rtjelum/esp32-ld19-lidar/sokoban_levels.h

#pragma once

// Sokoban level data, '|'-separated, kept in flash (PROGMEM).
// Map symbols: '#' wall, ' ' floor, '.' goal, '$' box, '*' box on goal,
//              '@' player, '+' player on goal.
//
// Each level sits in its own raw-string block so the playfield reads as
// ASCII art in source — adjacent string literals concatenate, and the
// "|" between blocks is the run-time level separator.
//
// NOTE: currently unused by the firmware. The Sokoban page in sokoban_page.h
// ships its own copy of the levels in JS. Kept here for a future native
// renderer that would draw the game on the AMOLED.

#ifndef PROGMEM
#define PROGMEM
#endif

static const char ZK_LEVEL_DATA[] PROGMEM =
  // ── Level 1 ──
  R"(####
# .#
#  ###
#*@  #
#  $ #
#  ###
####)"
  "|"
  // ── Level 2 ──
  R"(######
#    #
# #@ #
# $* #
# .* #
#    #
######)"
  "|"
  // ── Level 3 ──
  R"(  ####
###  ####
#     $ #
# #  #$ #
# . .#@ #
#########)"
  "|"
  // ── Level 4 ──
  R"(########
#      #
# .**$@#
#      #
#####  #
    ####)"
  "|"
  // ── Level 5 ──
  R"( #######
 #     #
 # .$. #
## $@$ #
 #  .$. #
#      #
########)"
  "|"
  // ── Level 6 ──
  R"(###### #####
#    ###   #
# $$     #@#
# $ #...   #
#   ########
#####)"
  "|"
  // ── Level 7 ──
  R"(#######
#     #
# .$. #
# $.$ #
# .$. #
# $.$ #
#  @  #
#######)"
  "|"
  // ── Level 8 ──
  R"(  ######
  # ..@#
  # $$ #
  ## ###
   # #
   # #
#### #
#    ##
# #   #
#   # #
###   #
  #####)"
  "|"
  // ── Level 9 ──
  R"(#####
#.  ##
#@$$ #
##   #
 ##  #
  ##.#
   ###)"
  "|"
  // ── Level 10 ──
  R"(      #####
      #.  #
      #.# #
#######.# #
# @ $ $ $ #
# # # # ###
#       #
#########)"
  "|"
  // ── Level 11 ──
  R"(  ######
  #    #
  # ##@##
### # $ #
# ..# $ #
#       #
#  ######
####)"
  "|"
  // ── Level 12 ──
  R"(#####
#   ##
# $  #
## $ ####
 ###@.  #
  #  .# #
  #     #
  #######)"
  "|"
  // ── Level 13 ──
  R"(####
#. ##
#.@ #
#. $#
##$ ###
 # $  #
 #    #
 #  ###
 ####)"
  "|"
  // ── Level 14 ──
  R"(#######
#     #
# # # #
#. $*@#
#   ###
#####)"
  "|"
  // ── Level 15 ──
  R"(     ###
######@##
#    .* #
#   #   #
#####$# #
    #   #
    #####)"
  "|"
  // ── Level 16 ──
  R"( ####
 #  ####
 #     ##
## ##   #
#. .# @$##
#   # $$ #
#  .#    #
##########)"
  "|"
  // ── Level 17 ──
  R"(#####
# @ #
#...#
#$$$##
#    #
#    #
######)"
  "|"
  // ── Level 18 ──
  R"(#######
#     #
#. .  #
# ## ##
#  $ #
###$ #
  #@ #
  #  #
  ####)"
  "|"
  // ── Level 19 ──
  R"(########
#   .. #
#  @$$ #
##### ##
   #  #
   #  #
   #  #
   ####)"
  "|"
  // ── Level 20 ──
  R"(#######
#     ###
#  @$$..#
#### ## #
  #     #
  #  ####
  #  #
  ####)"
  "|"
  // ── Level 21 ──
  R"(####
#  ####
# . . #
# $$#@#
##    #
 ######)"
  "|"
  // ── Level 22 ──
  R"(#####
#   ###
#. .  #
#   # #
## #  #
 #@$$ #
 #    #
 #  ###
 ####)"
  "|"
  // ── Level 23 ──
  R"(#######
#  *  #
#     #
## # ##
 #$@.#
 #   #
 #####)"
  "|"
  // ── Level 24 ──
  R"(# #####
  #   #
###$$@#
#   ###
#     #
# . . #
#######)"
  "|"
  // ── Level 25 ──
  R"( ####
 #  ###
 # $$ #
##... #
#  @$ #
#   ###
#####)"
  "|"
  // ── Level 26 ──
  R"( #####
 # @ #
 #   #
###$ #
# ...#
# $$ #
###  #
  ####)"
  "|"
  // ── Level 27 ──
  R"(######
#   .#
# ## ##
#  $$@#
# #   #
#.  ###
#####)"
  "|"
  // ── Level 28 ──
  R"(#####
#   #
# @ #
# $$###
##. . #
 #    #
 ######)"
  "|"
  // ── Level 29 ──
  R"(     #####
     #   ##
     #    #
 ######   #
##     #. #
# $ $ @  ##
# ######.#
#        #
##########)"
  "|"
  // ── Level 30 ──
  R"(####
#  ###
# $$ #
#... #
# @$ #
#   ##
#####)"
  "|"
  // ── Level 31 ──
  R"(  ####
 ##  #
##@$.##
# $$  #
# . . #
###   #
  #####)"
  "|"
  // ── Level 32 ──
  R"( ####
##  ###
#     #
#.**$@#
#   ###
##  #
 ####)"
  "|"
  // ── Level 33 ──
  R"(#######
#. #  #
#  $  #
#. $#@#
#  $  #
#. #  #
#######)"
  "|"
  // ── Level 34 ──
  R"(  ####
###  ####
#       #
#@$***. #
#       #
#########)"
  "|"
  // ── Level 35 ──
  R"(  ####
 ##  #
 #. $#
 #.$ #
 #.$ #
 #.$ #
 #. $##
 #   @#
 ##   #
  #####)"
  "|"
  // ── Level 36 ──
  R"(####
#  ############
# $ $ $ $ $ @ #
# .....       #
###############)"
  "|"
  // ── Level 37 ──
  R"(      ###
##### #.#
#   ###.#
#   $ #.#
# $  $  #
#####@# #
    #   #
    #####)"
  "|"
  // ── Level 38 ──
  R"(##########
#        #
# ##.### #
# # $$ . #
# . @$## #
#####    #
    ######)"
  "|"
  // ── Level 39 ──
  R"(#####
#   ####
# # # .#
#    $ ###
### #$.  #
#   #@   #
# # ######
#   #
#####)"
  "|"
  // ── Level 40 ──
  R"( #####
 #   #
##   ##
# $$$ #
# .+. #
#######)"
  "|"
  // ── Level 41 ──
  R"(#######
#     #
#@$$$ ##
#  #...#
##    ##
 ######)"
  "|"
  // ── Level 42 ──
  R"(   ####
   #  #
   #@ #
####$.#
#   $.#
# # $.#
#    ##
######)"
  "|"
  // ── Level 43 ──
  R"(     ####
     # @#
     #  #
###### .#
#   $  .#
#  $$# .#
#    ####
###  #
  ####)"
  "|"
  // ── Level 44 ──
  R"(#####
#@$.#
#####)"
  "|"
  // ── Level 45 ──
  R"(######
#... #
#  $ #
# #$##
#  $ #
#  @ #
######)"
  "|"
  // ── Level 46 ──
  R"( ######
##    #
#  ## #
# # $ #
#  * .#
## #@##
 #   #
 #####)"
  "|"
  // ── Level 47 ──
  R"(  #######
###     #
# $ $   #
# ### #####
# @ . .   #
#   ###   #
##### #####)"
  "|"
  // ── Level 48 ──
  R"(######
#  @ #
#  # ##
# .#  ##
# .$$$ #
# .#   #
####   #
   #####)"
  "|"
  // ── Level 49 ──
  R"(######
# @  #
# $# #
# $  #
# $ ##
### ####
 #  #  #
 #...  #
 #     #
 #######)"
  "|"
  // ── Level 50 ──
  R"(  ####
###  #####
#  $  @..#
# $    # #
### #### #
  #      #
  ########)"
  ;
